ouser555/ergoknife2touch/pic/003.jpg

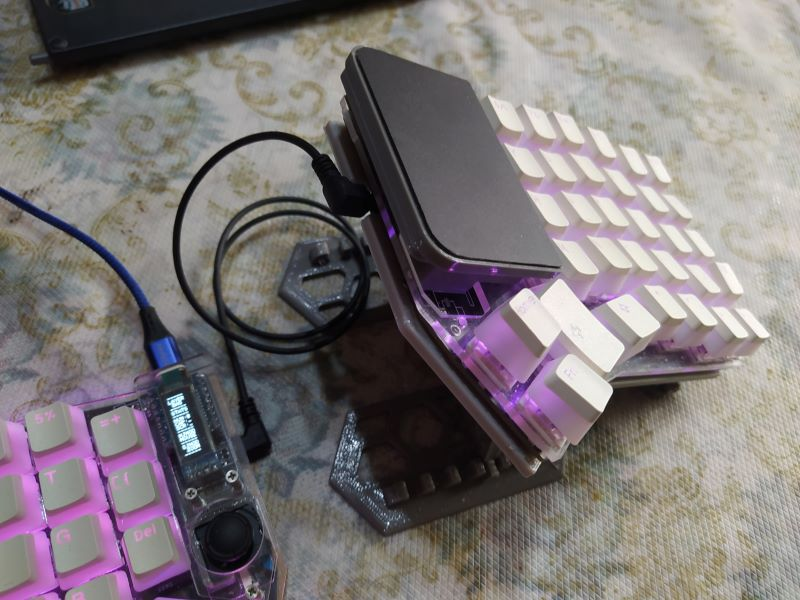
pic/003.jpg
