ouser555/ergoknife2touch/pic/005.jpg

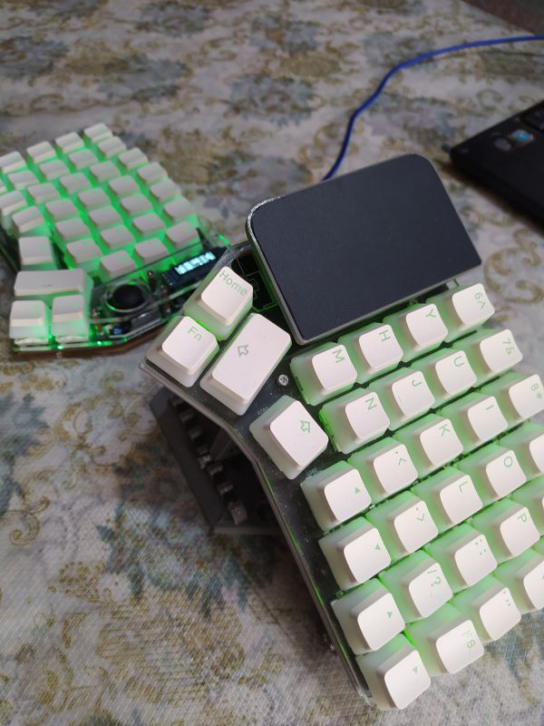
pic/005.jpg
